madworm/Youyue-858D-plus-FAN-speed-mod/Docs/04-remove-R3.png

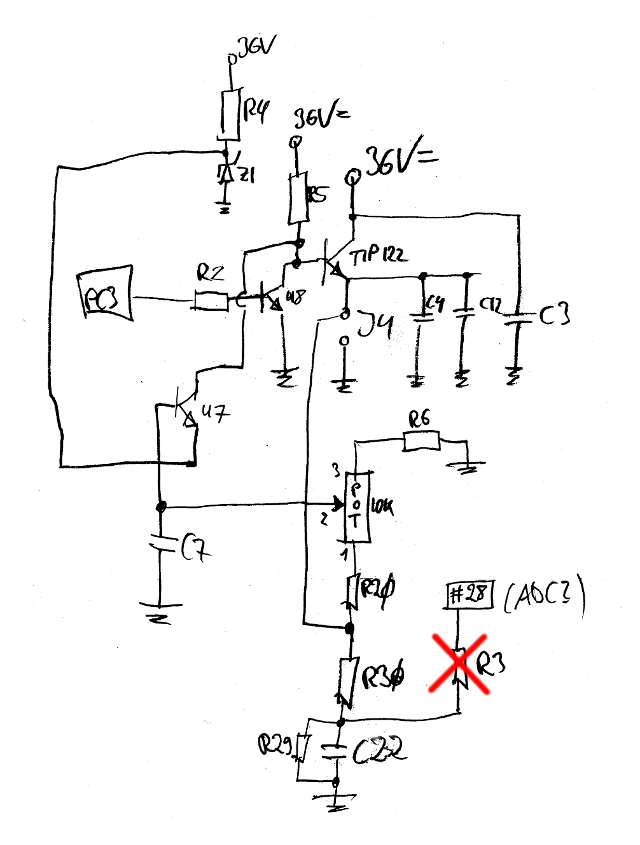
Docs/04-remove-R3.png
