madworm/Youyue-858D-plus-FAN-speed-mod/Docs/06-spacers.jpg

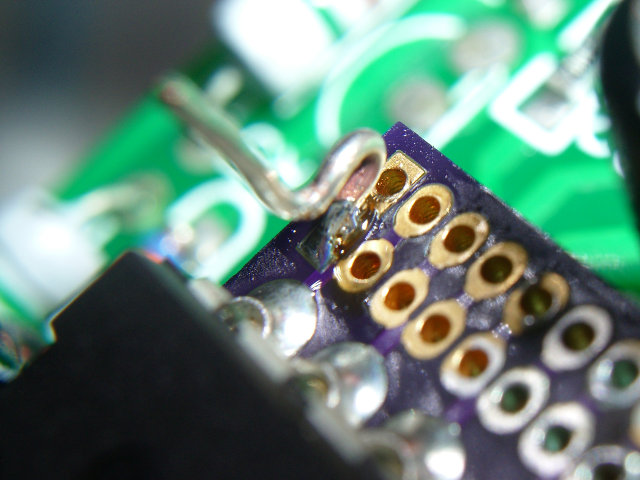
Docs/06-spacers.jpg
