madworm/Youyue-858D-plus-FAN-speed-mod/Docs/09-raw-BLDC-signal.jpg

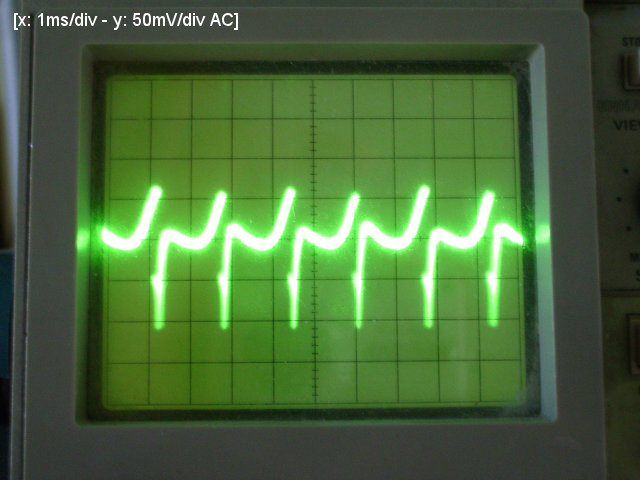
Docs/09-raw-BLDC-signal.jpg
