madworm/Youyue-858D-plus-FAN-speed-mod/Docs/10-raw-BLDC-signal.jpg

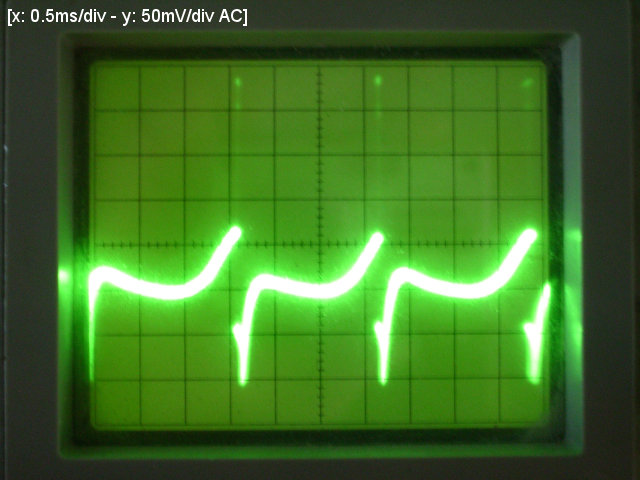
Docs/10-raw-BLDC-signal.jpg
