madworm/Youyue-858D-plus-FAN-speed-mod/Docs/11-after-comparator.jpg

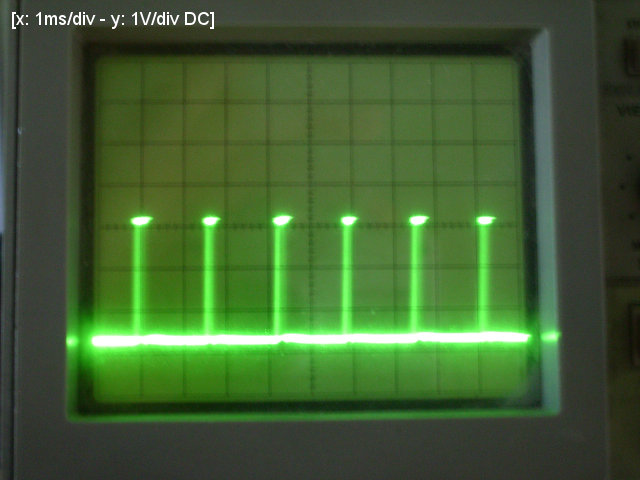
Docs/11-after-comparator.jpg
