madworm/Youyue-858D-plus-FAN-speed-mod/gerber_files/PNGs/youyue-858d-plus-fan-speed-mod.drl.png

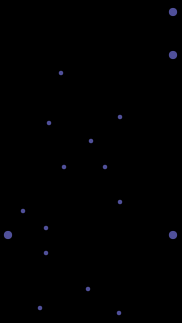
gerber_files/PNGs/youyue-858d-plus-fan-speed-mod.drl.png
