madworm/Youyue-858D-plus-FAN-speed-mod/gerber_files/PNGs/youyue-858d-plus-fan-speed-mod__front_purple.png

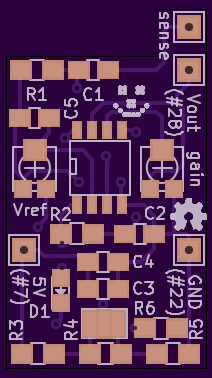
gerber_files/PNGs/youyue-858d-plus-fan-speed-mod__front_purple.png
