madworm/Youyue-858D-plus-FAN-speed-mod/Docs/07-testfit.jpg

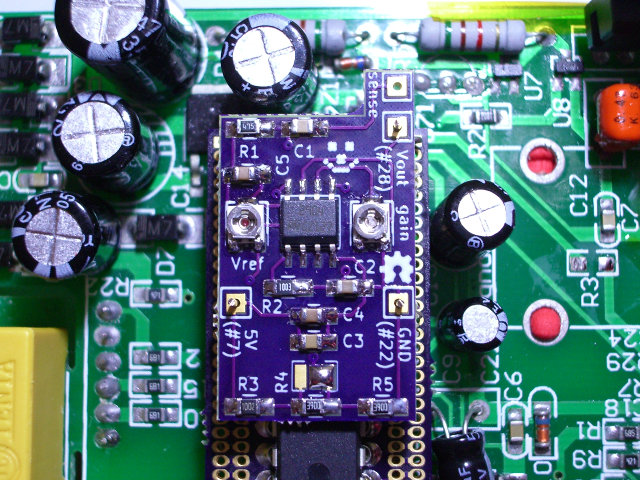
Docs/07-testfit.jpg
